ayumu-bekki/ardf_144_receiver/app/ardf_receiver/main/logger.h

#ifndef BFOX_RECEIVER_MAIN_LOGGER_H_
#define BFOX_RECEIVER_MAIN_LOGGER_H_
// ESP32 B-Fox Receiver
// (C)2025 bekki.jp

// Include ----------------------
#include <esp_log.h>

// Enable all log levels up to Verbose at compile time
#undef LOG_LOCAL_LEVEL
#define LOG_LOCAL_LEVEL CONFIG_LOG_DEFAULT_LEVEL

namespace receiver_system {

/// Application Log Tag
static constexpr char kTag[] = "ARDFReceiver";

namespace logger {

void InitializeLogLevel();

}  // namespace logger
}  // namespace receiver_system

#endif  // BFOX_RECEIVER_MAIN_LOGGER_H_
